sp4c38/diy_power_bank/Circuit/BQ76920/TI Question Simplified Schematic.jpg

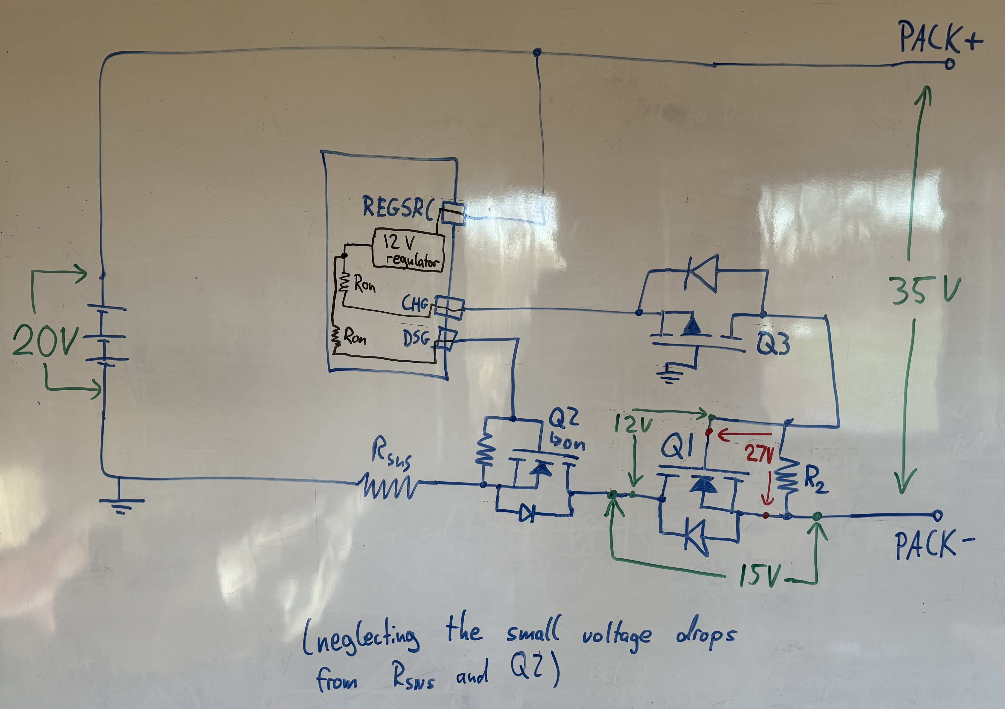
Circuit/BQ76920/TI Question Simplified Schematic.jpg
