sp4c38/diy_power_bank/Circuit/Other attempts/MAX1758/MAX1758_EVKIT.jpg

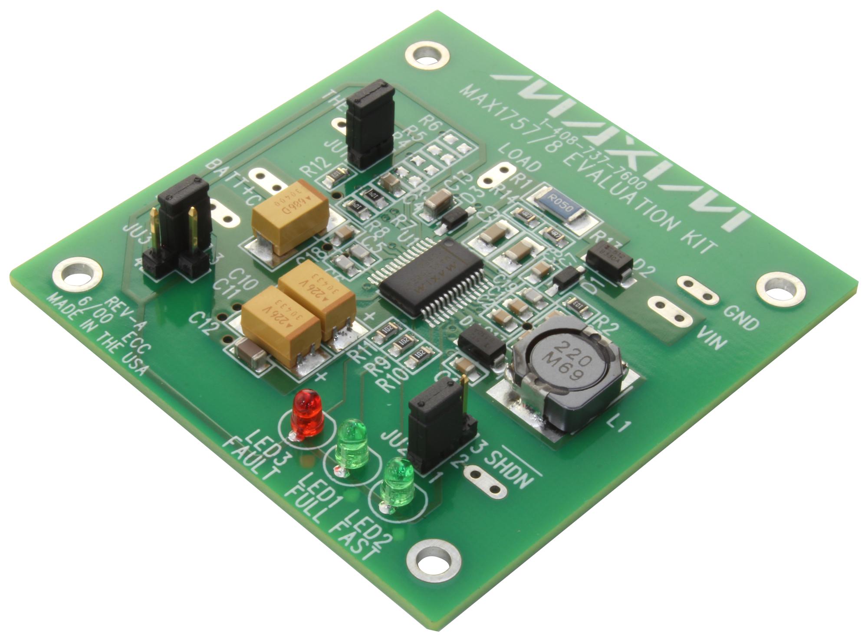
Circuit/Other attempts/MAX1758/MAX1758_EVKIT.jpg
