sp4c38/diy_power_bank/Circuit/PCB Renders/V3/Bottom View.png

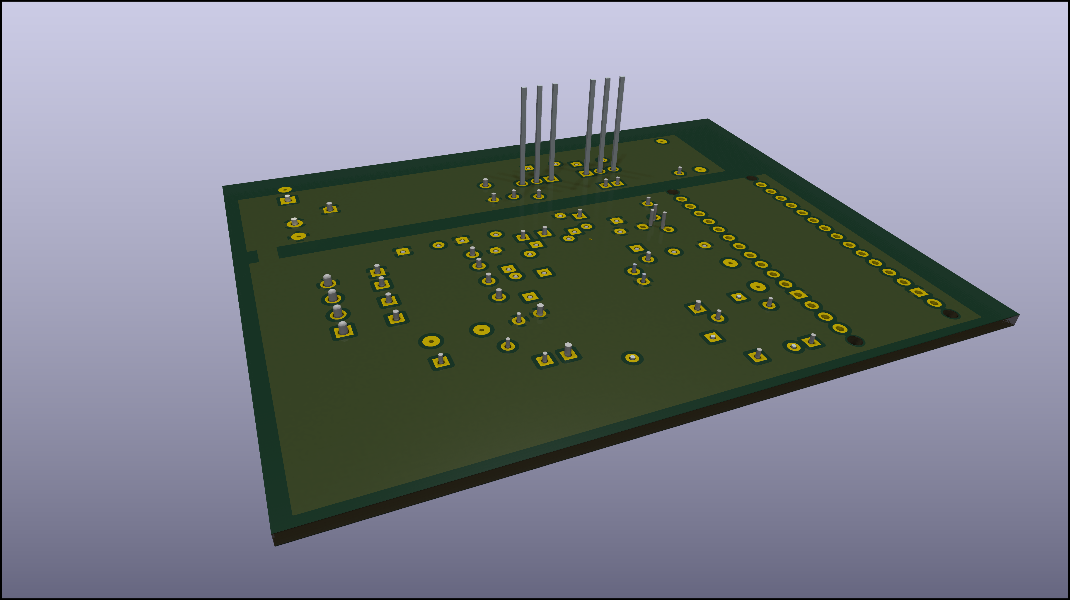
Circuit/PCB Renders/V3/Bottom View.png
