sp4c38/diy_power_bank/3D Printed Parts/Battery Holder/Try 1/Flexing_battery_holders_with_integrated_spring_456900/images/flexbatter21700x2.png

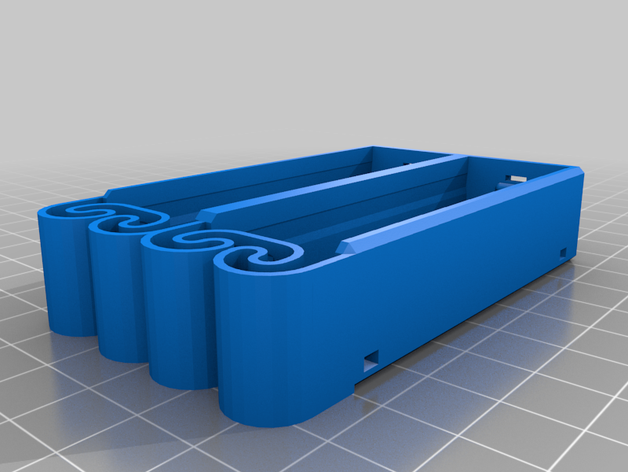
3D Printed Parts/Battery Holder/Try 1/Flexing_battery_holders_with_integrated_spring_456900/images/flexbatter21700x2.png
