sp4c38/diy_power_bank/3D Printed Parts/Battery Holder/Try 1/Flexing_battery_holders_with_integrated_spring_456900/files/flexbatter26650x1.stl

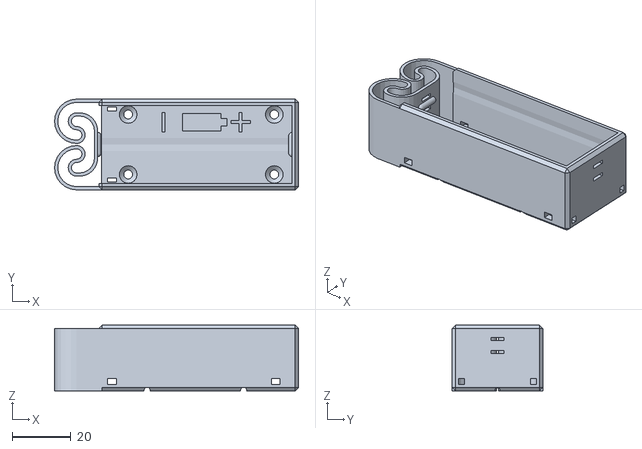
[picture p26: CAD file, 2023-12-29]
3D Printed Parts/Battery Holder/Try 1/Flexing_battery_holders_with_integrated_spring_456900/files/flexbatter26650x1.stl
83.0 x 30.9 x 22.4
