sp4c38/diy_power_bank/3D Printed Parts/Case/Base_Frame v169_Body116.stl

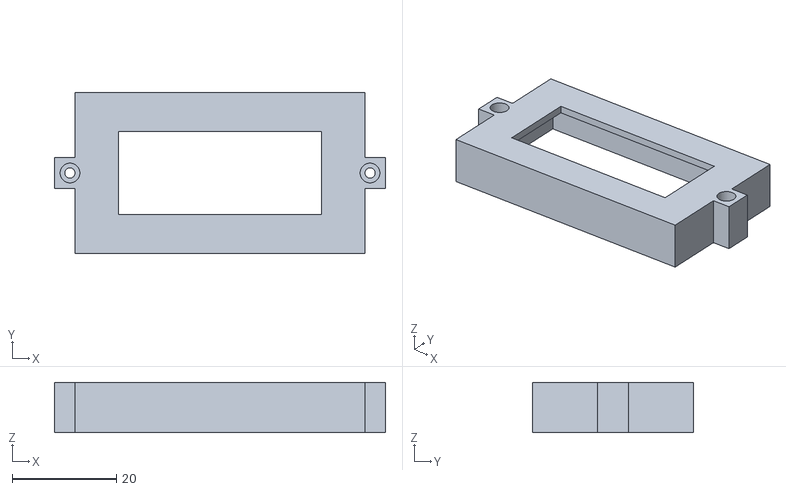
[picture p27: CAD file, 2026-07-05]
3D Printed Parts/Case/Base_Frame v169_Body116.stl
63.6 x 30.8 x 9.70
