sp4c38/diy_power_bank/3D Printed Parts/Battery Holder/Try 1/Flexing_battery_holders_with_integrated_spring_456900/files/flexbatter26650x3.stl

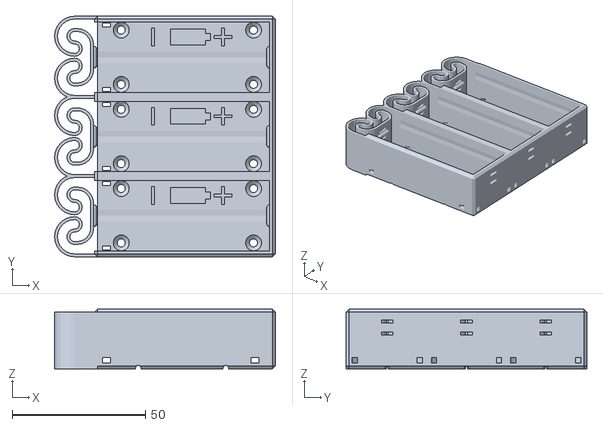
[picture p28: CAD file, 2023-12-29]
3D Printed Parts/Battery Holder/Try 1/Flexing_battery_holders_with_integrated_spring_456900/files/flexbatter26650x3.stl
83.0 x 90.4 x 22.4
