sp4c38/diy_power_bank/3D Printed Parts/Case/Base_Frame v169_Diode Cover.stl

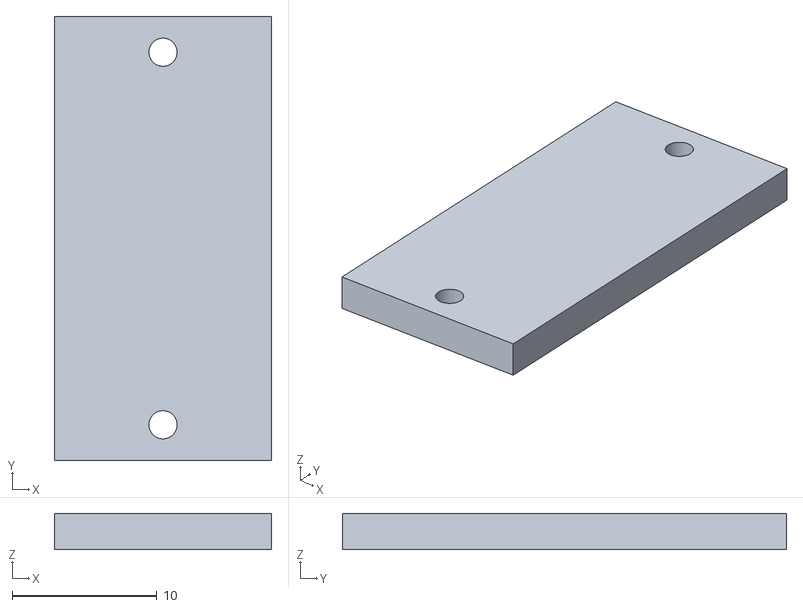
[picture p29: CAD file, 2026-07-05]
3D Printed Parts/Case/Base_Frame v169_Diode Cover.stl
15.0 x 30.7 x 2.50
