sp4c38/diy_power_bank/3D Printed Parts/Battery Holder/Try 1/Flexing_battery_holders_with_integrated_spring_456900/files/flexbatterCR123Ax2.stl

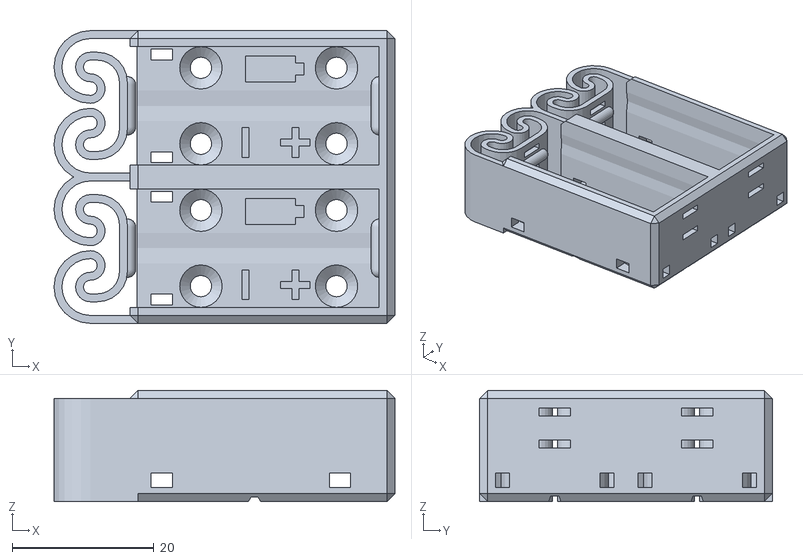
[picture p30: CAD file, 2023-12-29]
3D Printed Parts/Battery Holder/Try 1/Flexing_battery_holders_with_integrated_spring_456900/files/flexbatterCR123Ax2.stl
48.0 x 41.2 x 15.6
