sp4c38/diy_power_bank/3D Printed Parts/Case/Base_Frame v169_MOSFET Top.stl

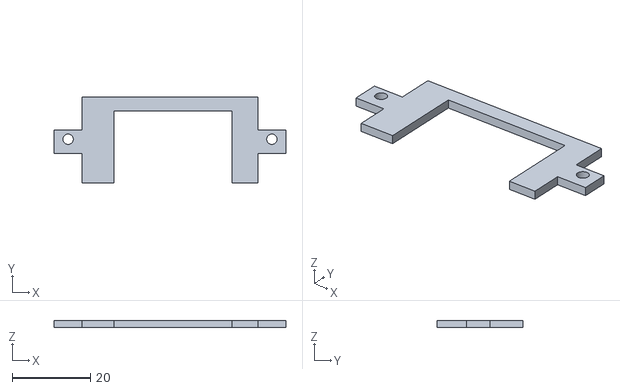
[picture p31: CAD file, 2026-07-05]
3D Printed Parts/Case/Base_Frame v169_MOSFET Top.stl
59.2 x 22.0 x 1.90
