sp4c38/diy_power_bank/3D Printed Parts/Battery Holder/Try 1/Flexing_battery_holders_with_integrated_spring_456900/files/flexbatterAAAx3.stl

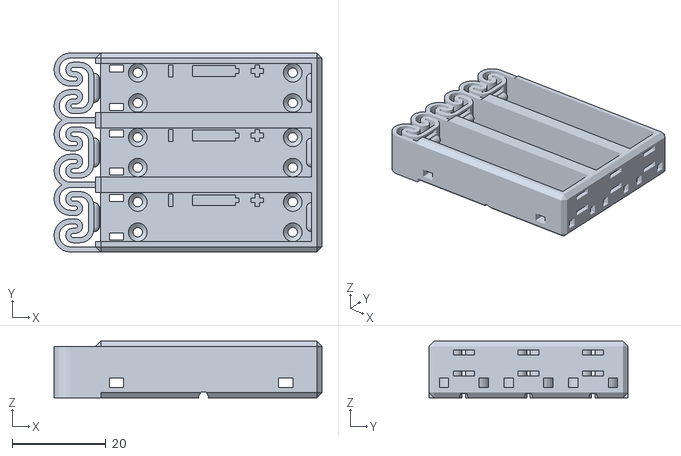
[picture p32: CAD file, 2023-12-29]
3D Printed Parts/Battery Holder/Try 1/Flexing_battery_holders_with_integrated_spring_456900/files/flexbatterAAAx3.stl
57.2 x 42.5 x 12.1
