sp4c38/diy_power_bank/3D Printed Parts/Battery Holder/Try 1/Flexing_battery_holders_with_integrated_spring_456900/files/flexbatterAAAx1.stl

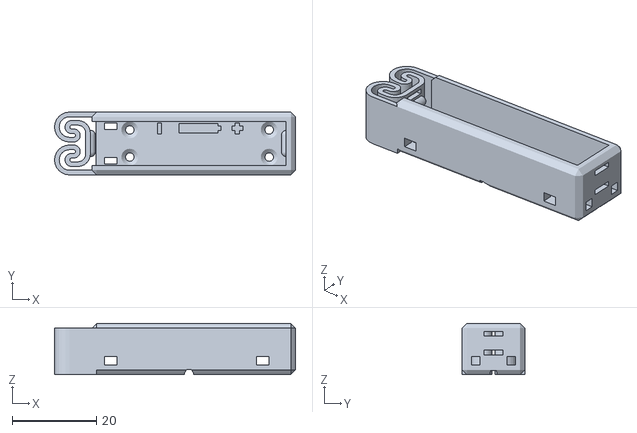
[picture p33: CAD file, 2023-12-29]
3D Printed Parts/Battery Holder/Try 1/Flexing_battery_holders_with_integrated_spring_456900/files/flexbatterAAAx1.stl
57.2 x 14.9 x 12.1
