sp4c38/diy_power_bank/Tutorials/Tutorial 1/20000 mAh 3.7V power bank data sheet.jpg

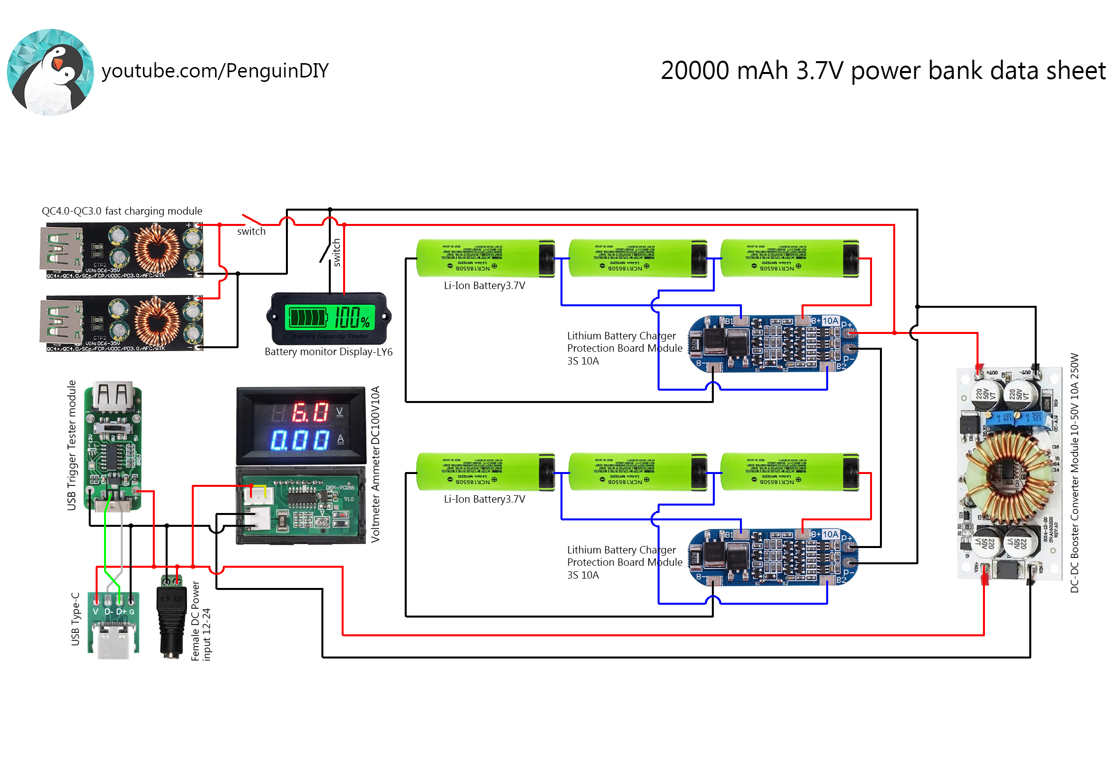
Tutorials/Tutorial 1/20000 mAh 3.7V power bank data sheet.jpg
