sp4c38/diy_power_bank/Circuit/KiCAD Circuit/Circuit_MAX1758.pdf

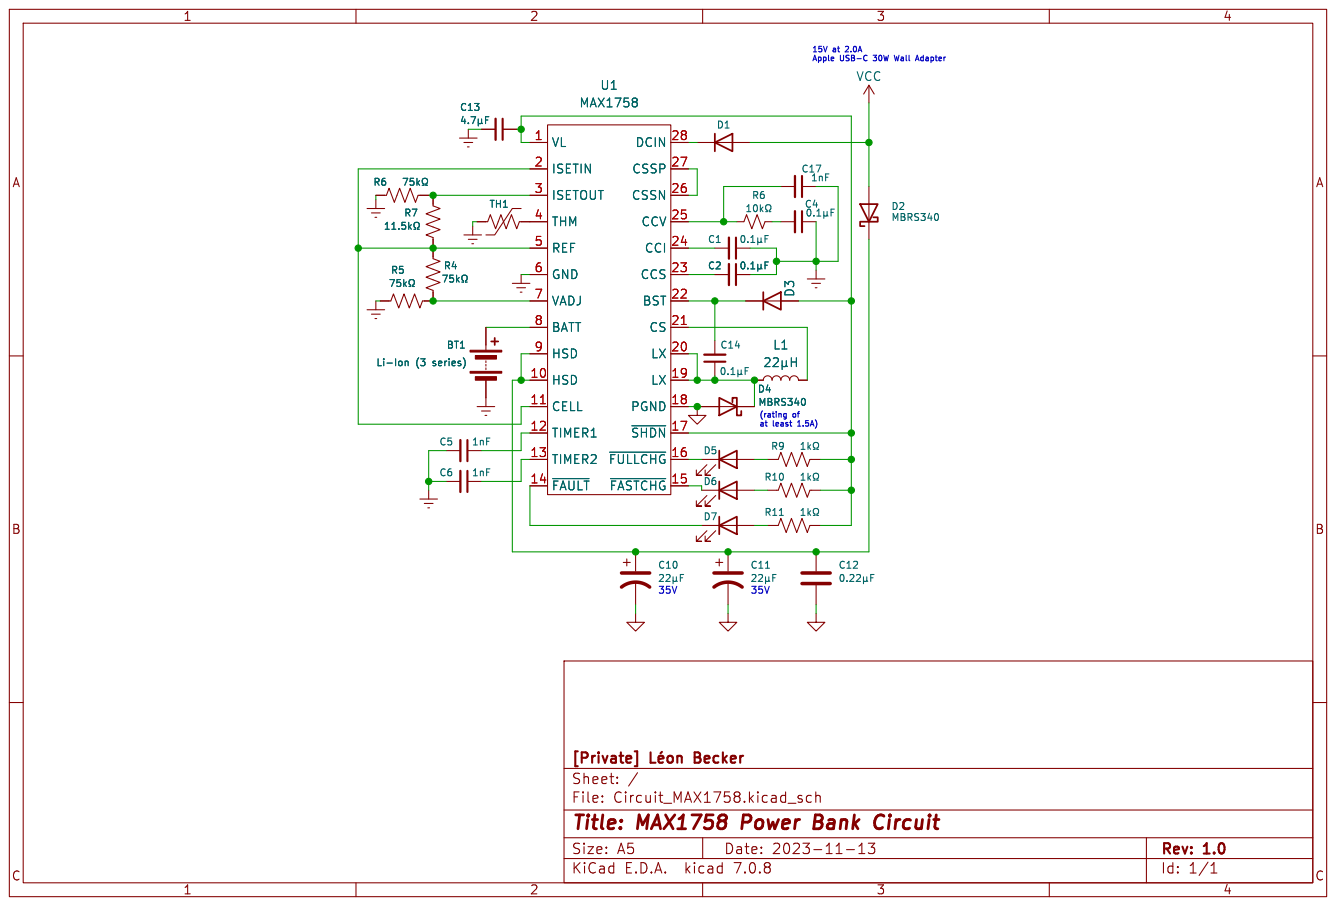
[picture p60: page 1]
