sp4c38/diy_power_bank/Code/PowerbankFirmware/powerManager.h

#ifndef POWER_MANAGER_H
#define POWER_MANAGER_H

#include <Arduino.h>

#include "register.h"
#include "safetyPolicy.h"

class PowerManager {
public:
    void noteOutputOn(ControlState& controls);
    void noteOutputOff(ControlState& controls);
    void update(const PackSnapshot& snapshot, ControlState& controls);
    unsigned long idleDurationMs() const;
    uint16_t idleRemainingSec(const PackSnapshot& snapshot, const ControlState& controls) const;
    bool automaticShutdownOccurred() const;
    /// Continue an idle stretch that was running before a reboot, so the
    /// very-long-idle ship countdown survives maintenance restarts.
    void restoreIdleElapsed(uint32_t seconds);

private:
    unsigned long lastActivityMs = 0;
    unsigned long idleCarryMs = 0;
    bool automaticShutdown = false;
};

#endif
